abhi-243/Satellite-Tracker/Files/PotGear.stl

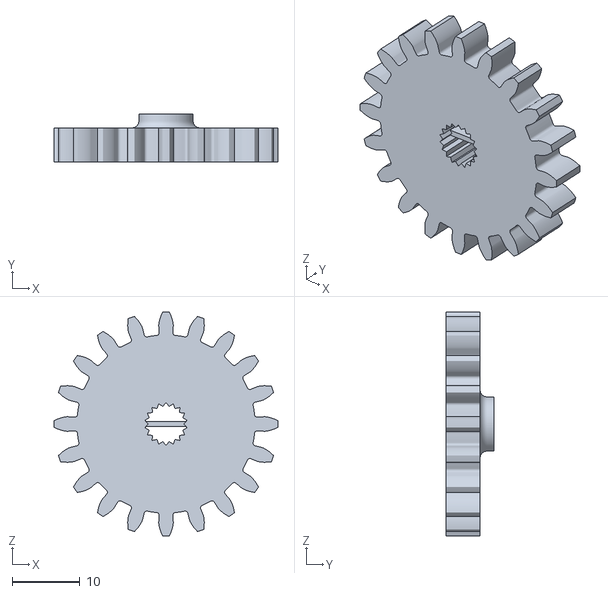
[picture p15: CAD file, 2025-02-25]
Files/PotGear.stl
33.0 x 7.00 x 33.0
