abhi-243/Satellite-Tracker/CAD Files/UHF+Connector.stp

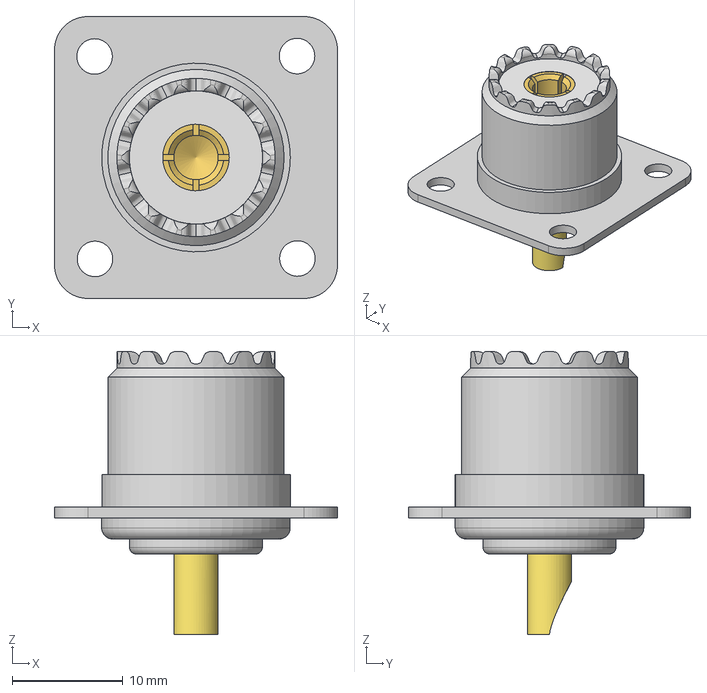
[picture p16: CAD file, 2025-02-25]
CAD Files/UHF+Connector.stp
25.5 x 25.4 x 25.5 mm
