abhi-243/Satellite-Tracker/Files/Claw.stl

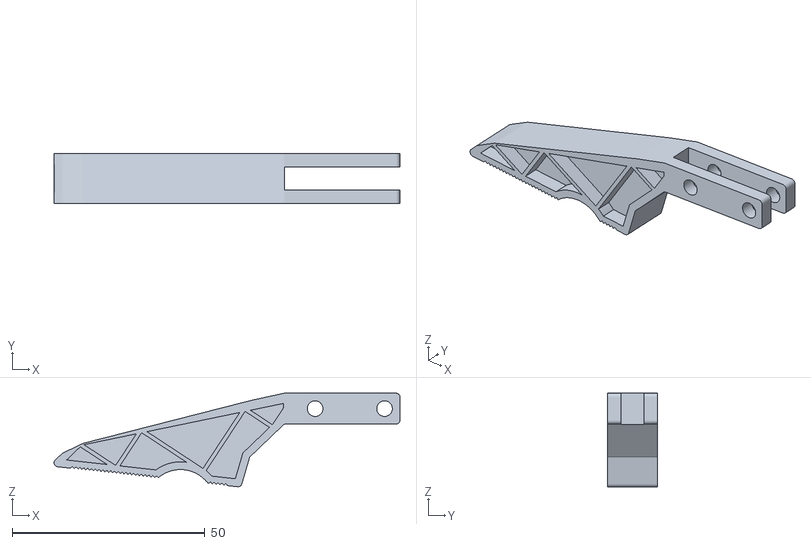
[picture p17: CAD file, 2025-02-25]
Files/Claw.stl
89.7 x 12.9 x 24.3
