abhi-243/Satellite-Tracker/CAD Files/Shaft+Collar.stp

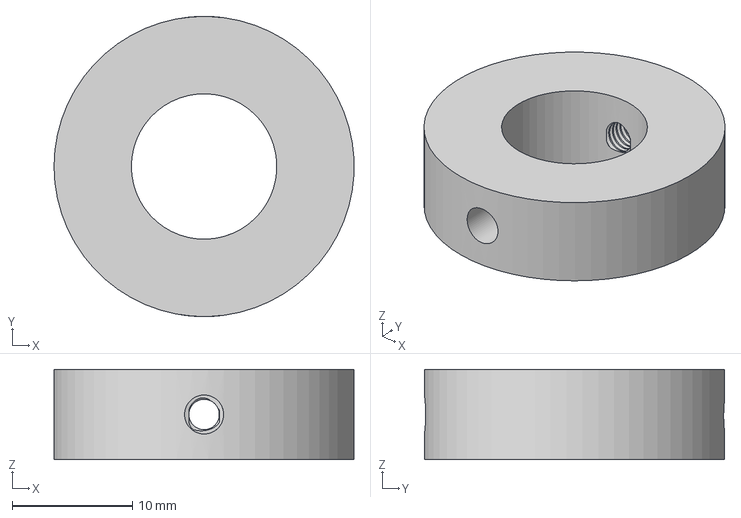
[picture p18: CAD file, 2025-02-25]
CAD Files/Shaft+Collar.stp
25.0 x 25.0 x 7.50 mm
