abhi-243/Satellite-Tracker/Files/PSU Lid.stl

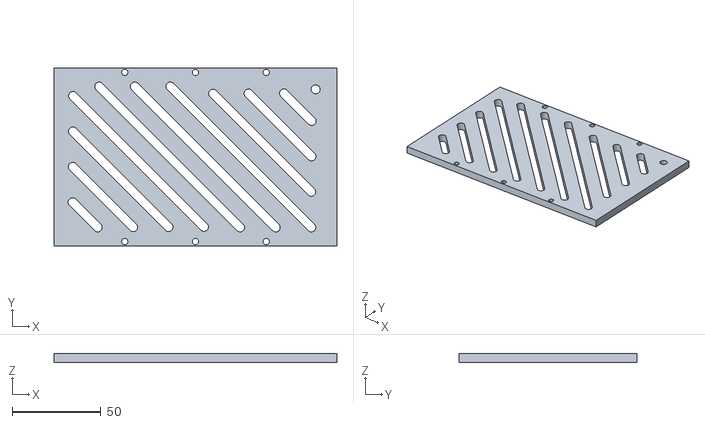
[picture p19: CAD file, 2025-02-25]
Files/PSU Lid.stl
159.0 x 100.0 x 5.00
