abhi-243/Satellite-Tracker/CAD Files/Yagi+2m_70cm.stp

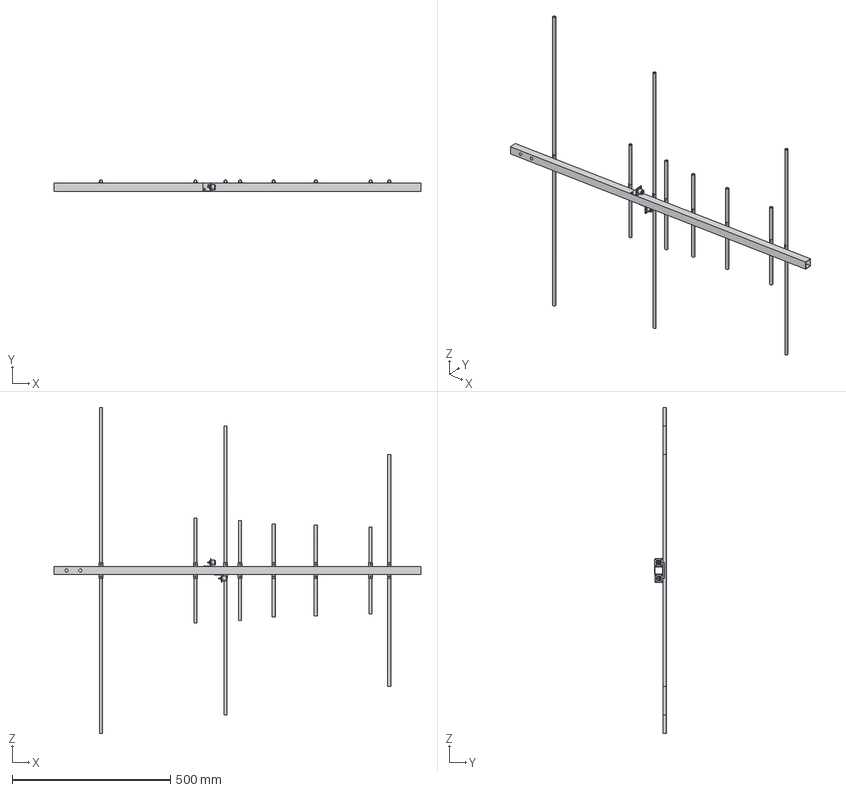
[picture p20: CAD file, 2025-02-25]
CAD Files/Yagi+2m_70cm.stp
1158.5 x 36.4 x 1029.8 mm
UHF Connector x 2
