abhi-243/Satellite-Tracker/Files/Connector_Gear.stl

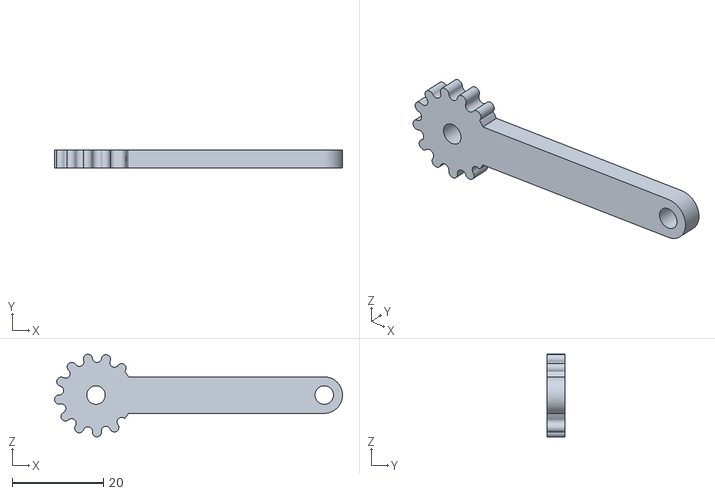
[picture p21: CAD file, 2025-02-25]
Files/Connector_Gear.stl
63.1 x 4.00 x 18.1
