abhi-243/Satellite-Tracker/CAD Files/Potentiometer.stp

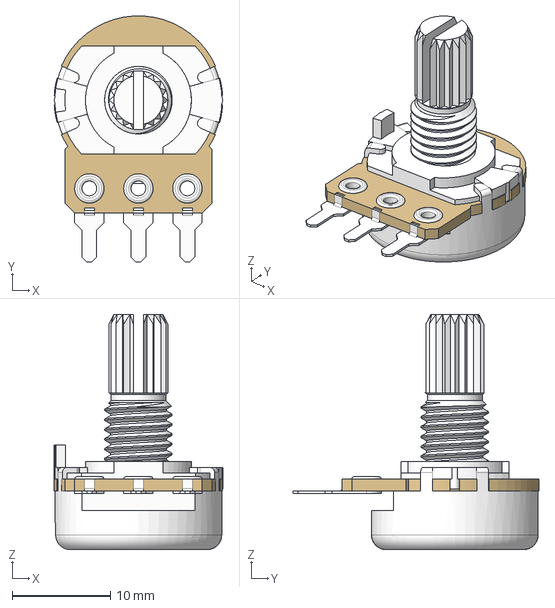
[picture p22: CAD file, 2025-02-25]
CAD Files/Potentiometer.stp
17.2 x 25.1 x 24.0 mm
