abhi-243/Satellite-Tracker/Files/Electronics Lid.stl

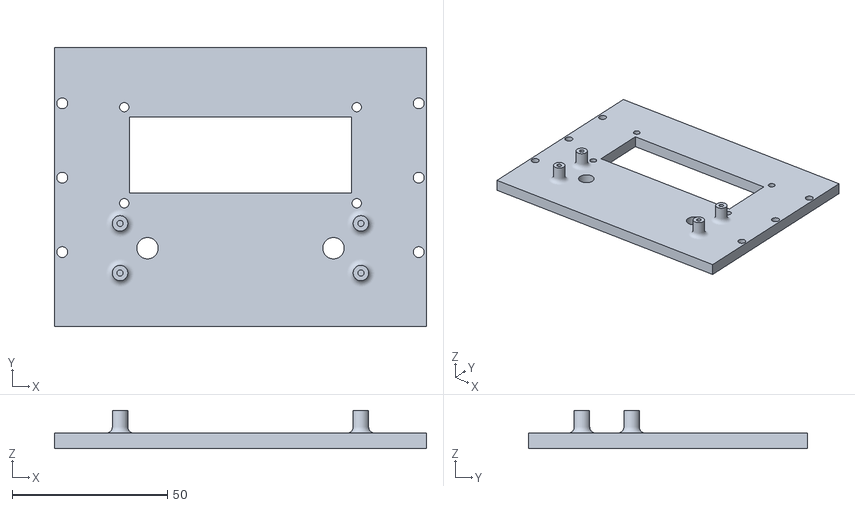
[picture p23: CAD file, 2025-02-25]
Files/Electronics Lid.stl
120.0 x 90.0 x 12.3
