abhi-243/Satellite-Tracker/CAD Files/5X8_COUPLER.stp

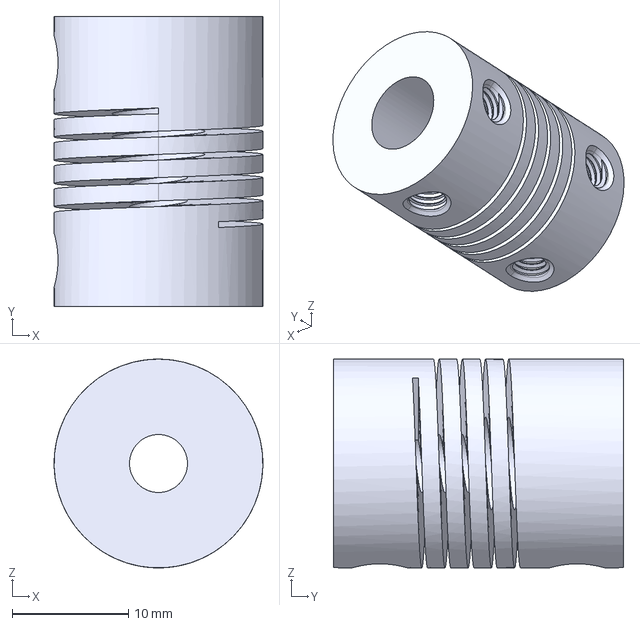
[picture p24: CAD file, 2025-02-25]
CAD Files/5X8_COUPLER.stp
18.0 x 25.0 x 18.0 mm
