abhi-243/Satellite-Tracker/Files/Rings.stl

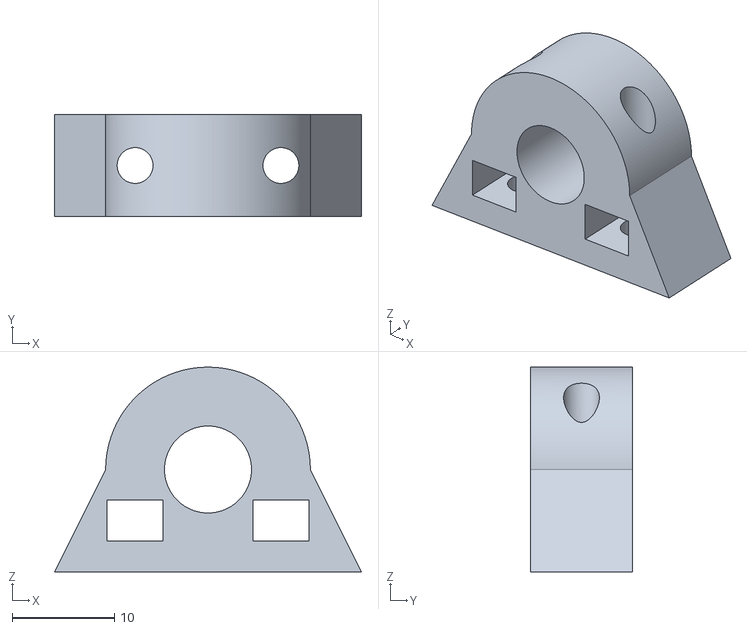
[picture p25: CAD file, 2025-02-25]
Files/Rings.stl
30.0 x 10.0 x 20.0
