abhi-243/Satellite-Tracker/Files/Base.stl

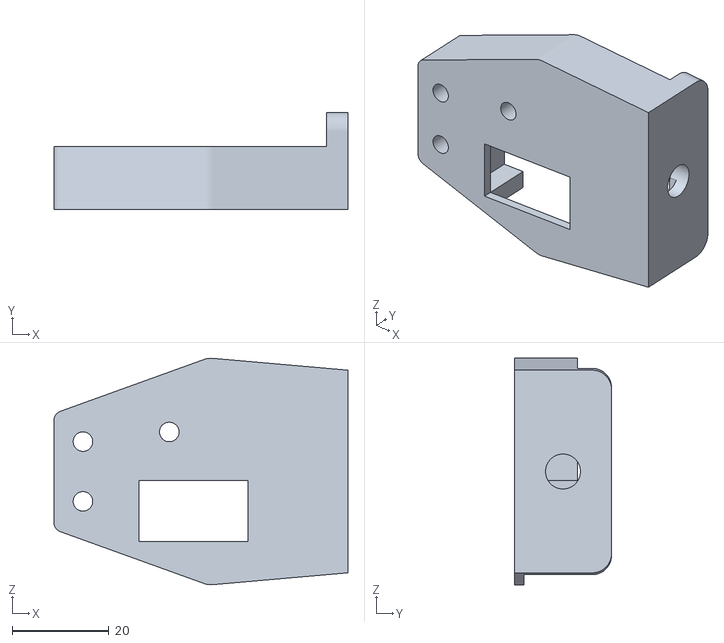
[picture p26: CAD file, 2025-02-25]
Files/Base.stl
60.9 x 20.1 x 46.9
