abhi-243/Satellite-Tracker/Files/Connector.stl

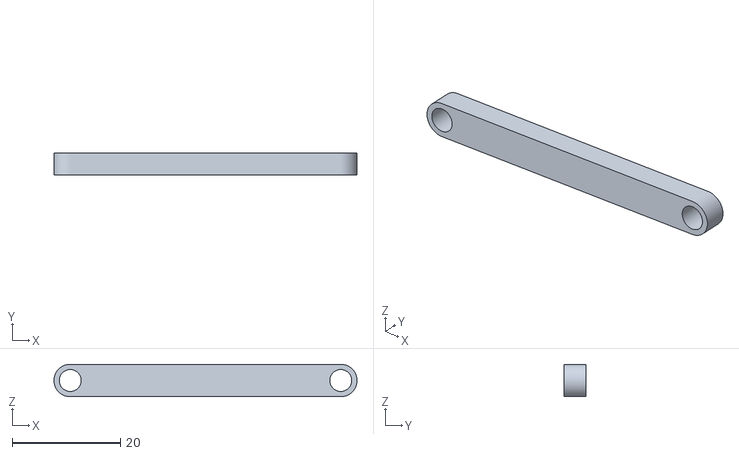
[picture p27: CAD file, 2025-02-25]
Files/Connector.stl
56.0 x 4.00 x 6.00
