abhi-243/Satellite-Tracker/Files/Electronics Box.stl

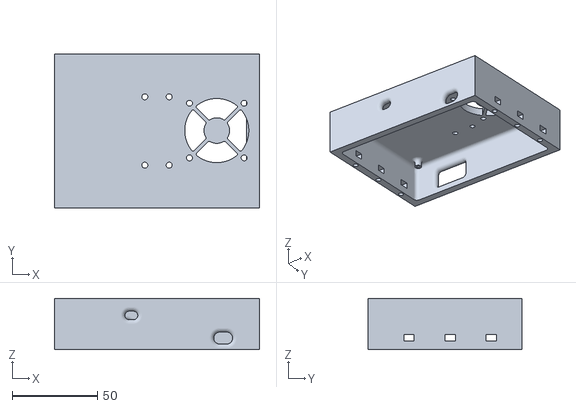
[picture p28: CAD file, 2025-02-25]
Files/Electronics Box.stl
120.0 x 90.0 x 30.0
