abhi-243/Satellite-Tracker/Files/PSU Box.stl

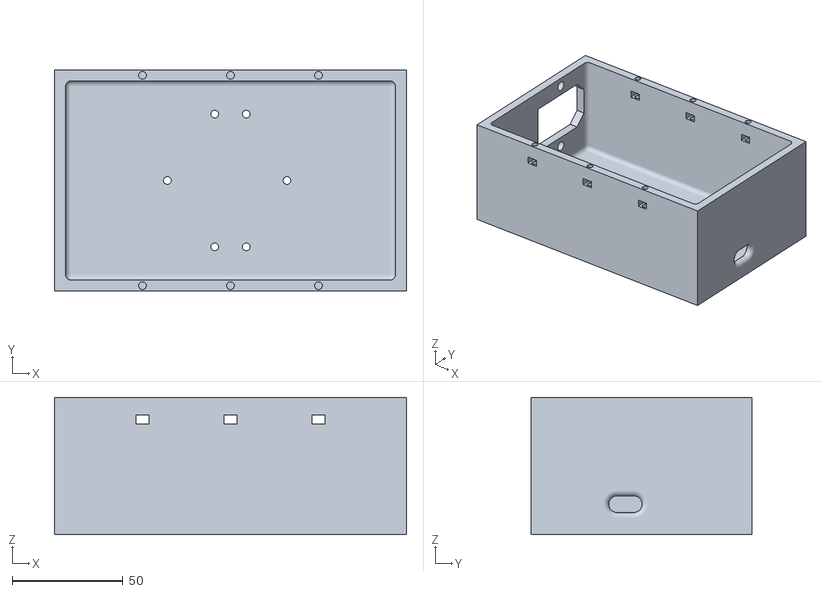
[picture p29: CAD file, 2025-02-25]
Files/PSU Box.stl
159.0 x 100.0 x 62.0
