abhi-243/Satellite-Tracker/Files/Azimuth Rotator.stl

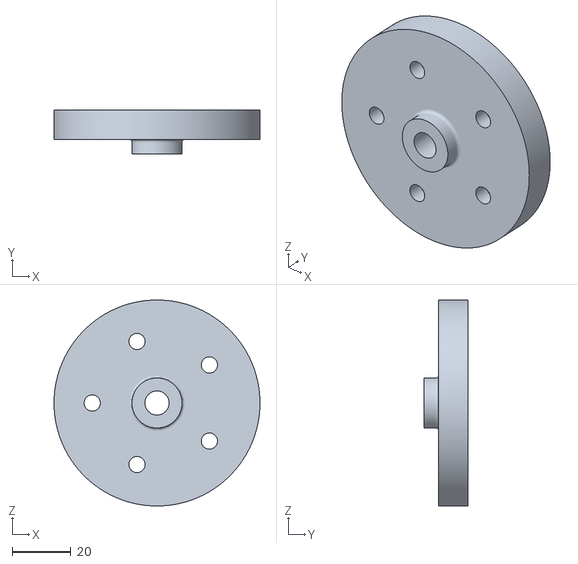
[picture p30: CAD file, 2025-02-25]
Files/Azimuth Rotator.stl
70.0 x 15.0 x 70.0
